zzeneg/zzkeeb/kicad/models/FPC 6-PIN SMD.stp

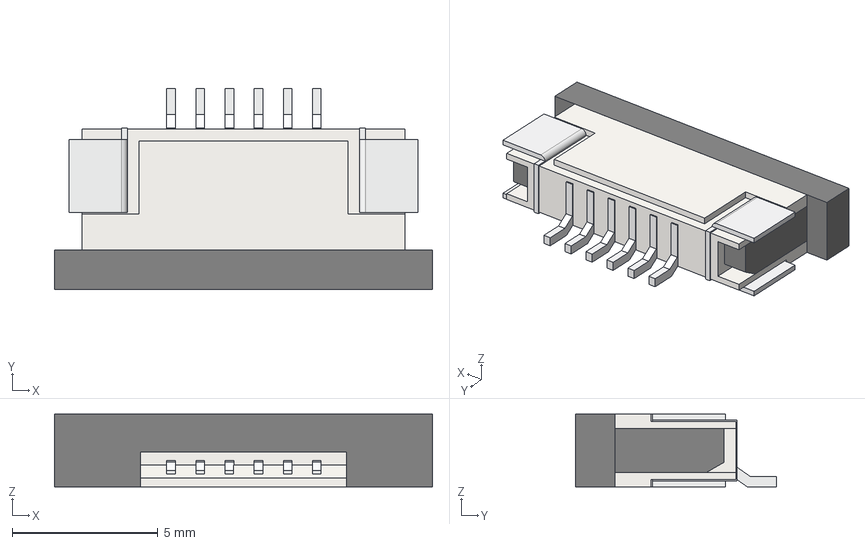
[picture p20: CAD file, 2024-02-03]
kicad/models/FPC 6-PIN SMD.stp
13.0 x 6.90 x 2.50 mm
