zzeneg/zzkeeb/kicad/models/vik-azoteq-adapter-vertical.step

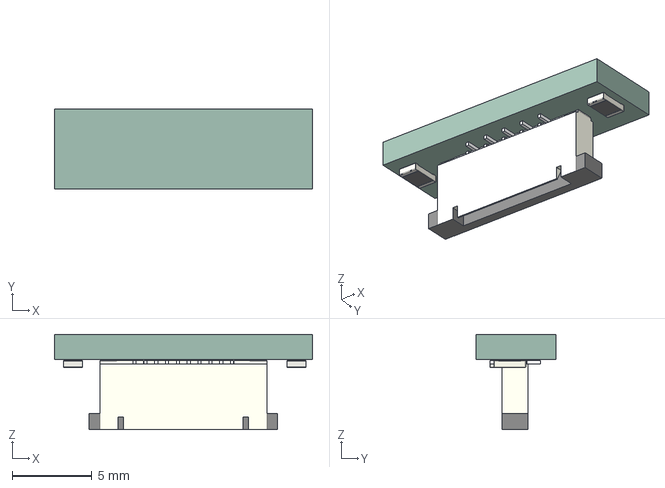
[picture p21: CAD file, 2024-02-03]
kicad/models/vik-azoteq-adapter-vertical.step
16.2 x 5.03 x 5.96 mm
_autosave-azoteq-tps PCB
