zzeneg/zzkeeb/kicad/models/PMW3360 v12.step

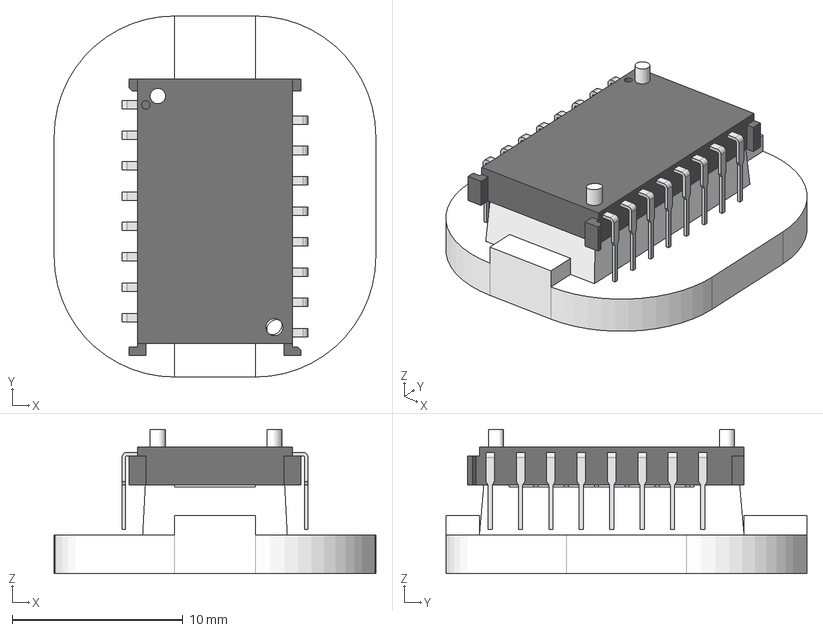
[picture p22: CAD file, 2024-01-15]
kicad/models/PMW3360 v12.step
18.9 x 21.1 x 8.46 mm
Lead x 8
Lead(Mirror) x 8
Lens
