zzeneg/zzkeeb/kicad/models/EC12 Encoder 10mm 3pin.stp

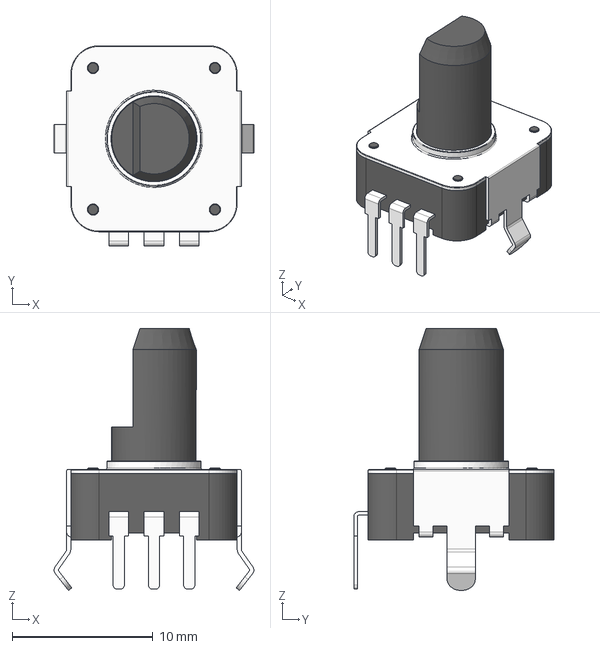
[picture p23: CAD file, 2023-12-11]
kicad/models/EC12 Encoder 10mm 3pin.stp
14.2 x 14.2 x 18.6 mm
