zzeneg/zzkeeb/kicad/models/Button_5way-SKRHABE010-concave-short.step

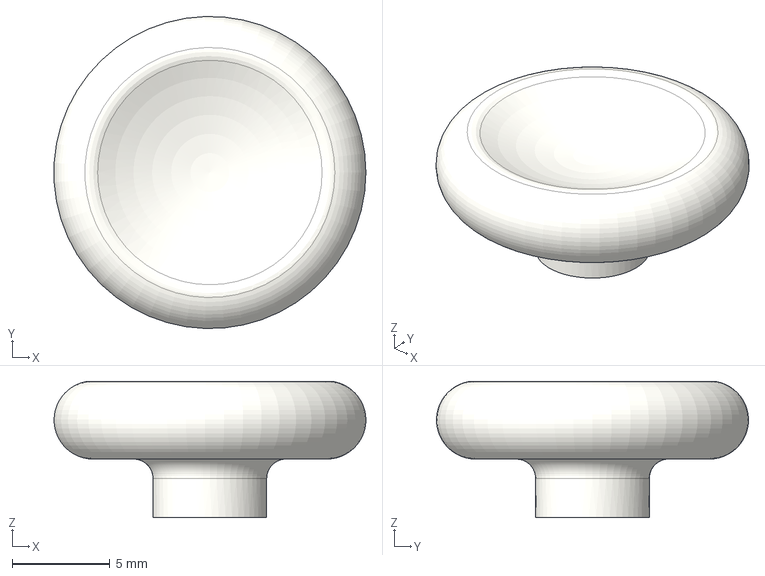
[picture p24: CAD file, 2023-11-05]
kicad/models/Button_5way-SKRHABE010-concave-short.step
16.0 x 16.0 x 6.98 mm
