zzeneg/zzkeeb/kicad/models/Button_5way-SKRHABE010.stp

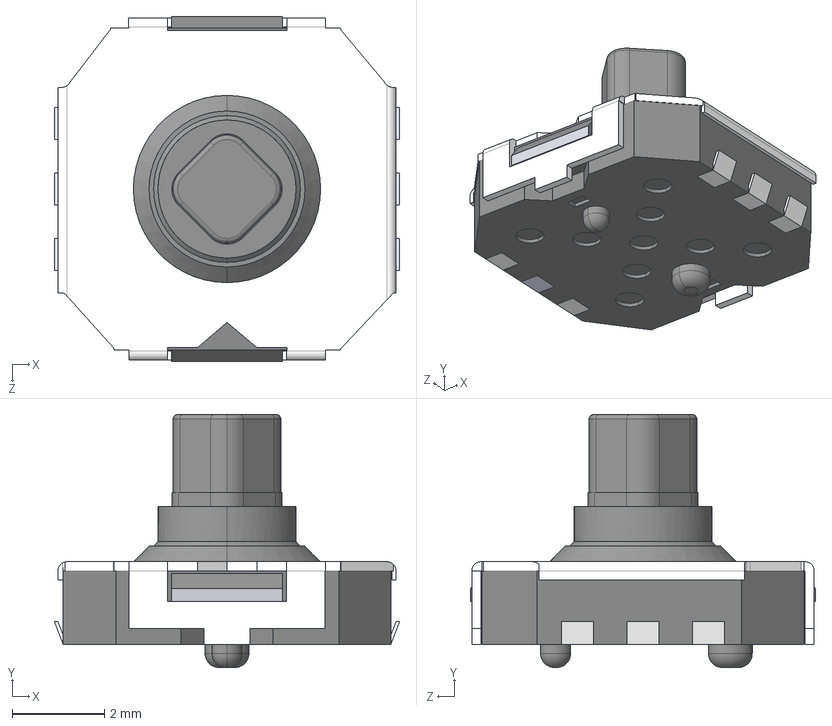
[picture p25: CAD file, 2023-11-05]
kicad/models/Button_5way-SKRHABE010.stp
7.51 x 5.50 x 7.50 mm
