zzeneg/zzkeeb/kicad/models/JST - GH - SMD (V) - 12Pin - 1.25mm.stp

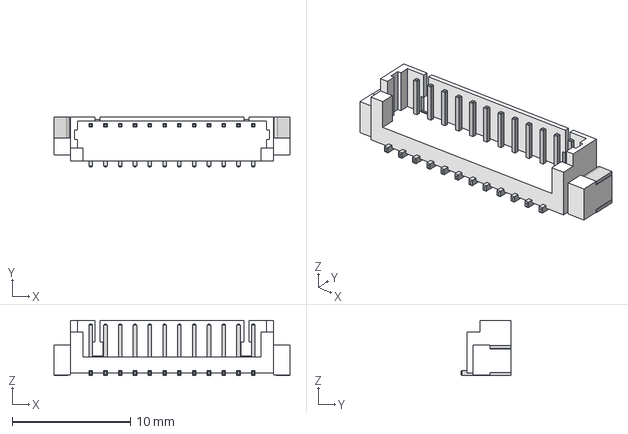
[picture p26: CAD file, 2023-11-02]
kicad/models/JST - GH - SMD (V) - 12Pin - 1.25mm.stp
19.9 x 4.24 x 4.66 mm
