zzeneg/zzkeeb/kicad/models/JST - GH - SMD (R) - 12Pin - 1.25mm.stp

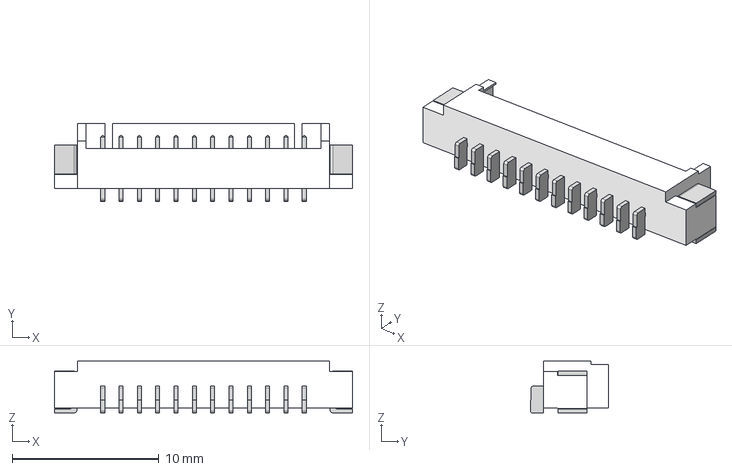
[picture p27: CAD file, 2023-11-02]
kicad/models/JST - GH - SMD (R) - 12Pin - 1.25mm.stp
20.3 x 5.35 x 3.53 mm
