zzeneg/zzkeeb/kicad/models/splinky.step

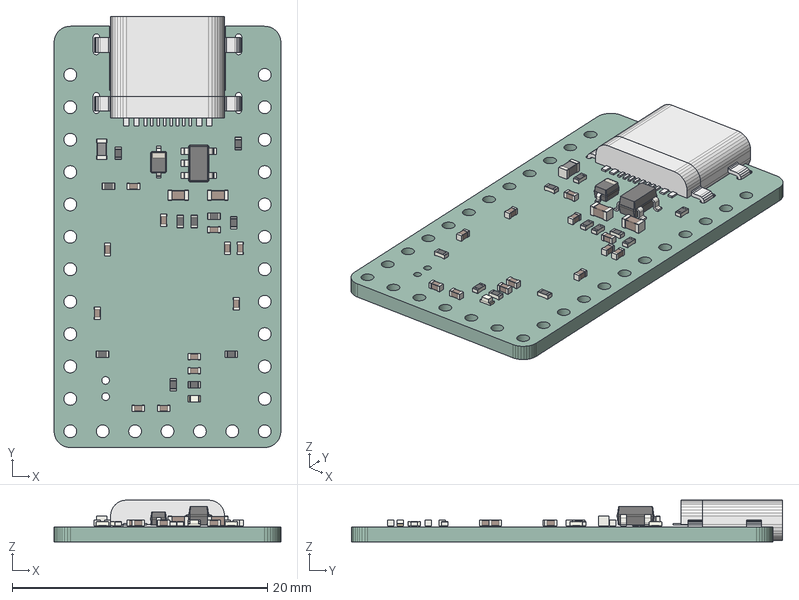
[picture p28: CAD file, 2023-11-01]
kicad/models/splinky.step
17.8 x 33.8 x 3.27 mm
0xB2 PCB
