zzeneg/zzkeeb/kicad/models/niceview.step

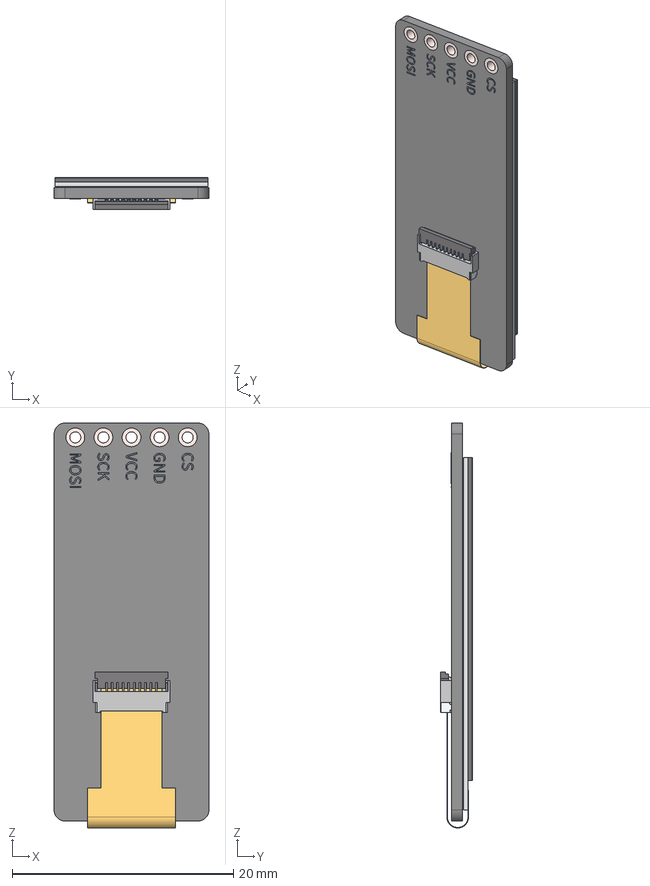
[picture p29: CAD file, 2023-11-01]
kicad/models/niceview.step
14.0 x 2.87 x 36.6 mm
Silkscreen
Screen
FPC
FFC2B28_SP x 2
FFC2B28-10-G_C
FFC2B28-G_P x 10
FFC2B28-10-G_H
FFC2B28-10-G_D
