zzeneg/zzkeeb/kicad/models/5-way-concave-short.step

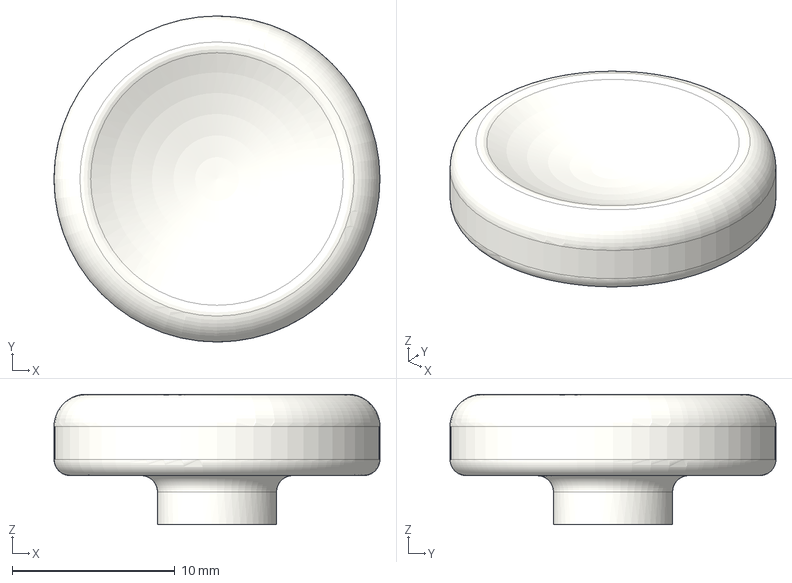
[picture p30: CAD file, 2023-09-16]
kicad/models/5-way-concave-short.step
20.0 x 20.0 x 7.98 mm
