zzeneg/zzkeeb/kicad/models/Magnetic connector 12pin female.step

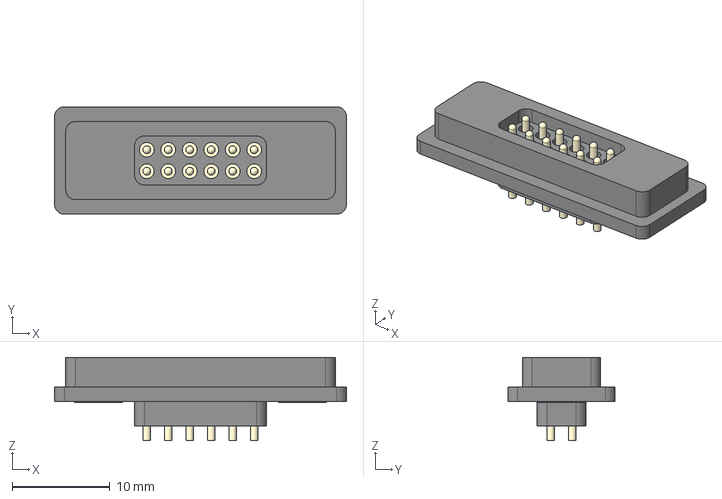
[picture p31: CAD file, 2023-09-04]
kicad/models/Magnetic connector 12pin female.step
29.9 x 11.0 x 8.50 mm
