zzeneg/zzkeeb/kicad/models/Magnetic connector 12pin male.step

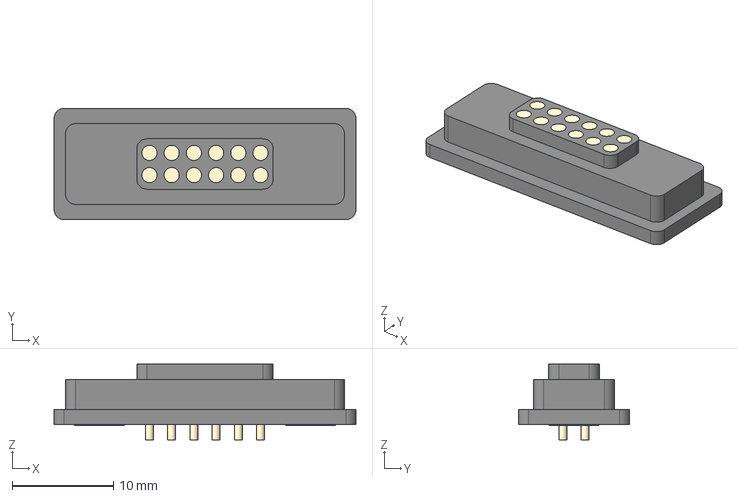
[picture p32: CAD file, 2023-09-04]
kicad/models/Magnetic connector 12pin male.step
29.9 x 11.0 x 7.50 mm
