zzeneg/zzkeeb/kicad/models/5-WayTactileButton10mmTHT.stp

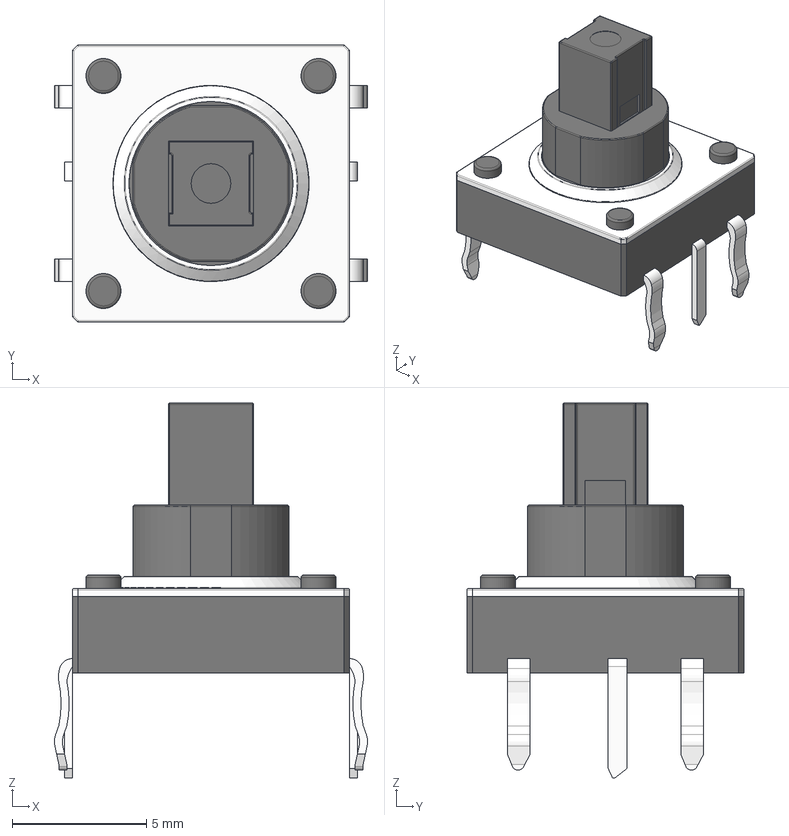
[picture p33: CAD file, 2023-08-19]
kicad/models/5-WayTactileButton10mmTHT.stp
11.6 x 10.3 x 14.0 mm
