zzeneg/zzkeeb/kicad/models/FPC-12.stp

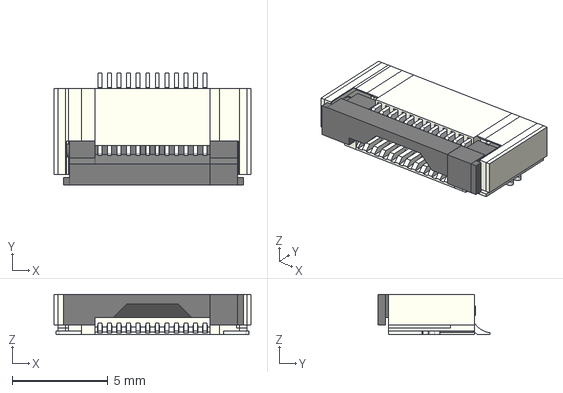
[picture p34: CAD file, 2023-06-14]
kicad/models/FPC-12.stp
10.3 x 5.85 x 2.11 mm
