zzeneg/zzkeeb/kicad/models/c-1-1734742-2-o-3d.stp

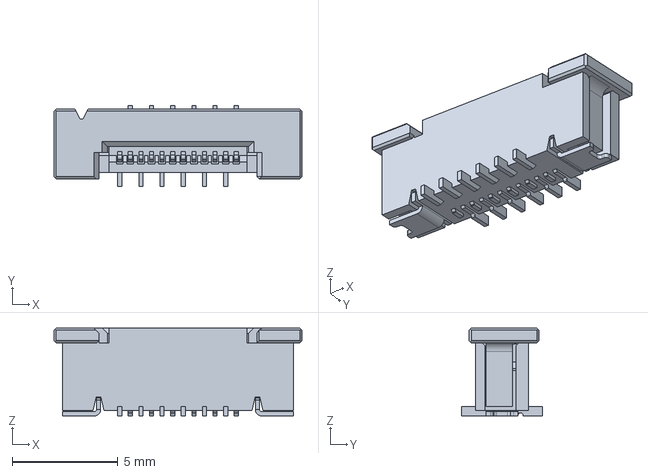
[picture p35: CAD file, 2023-06-14]
kicad/models/c-1-1734742-2-o-3d.stp
11.7 x 3.80 x 4.15 mm
