zzeneg/zzkeeb/kicad/models/ks33_socket.step

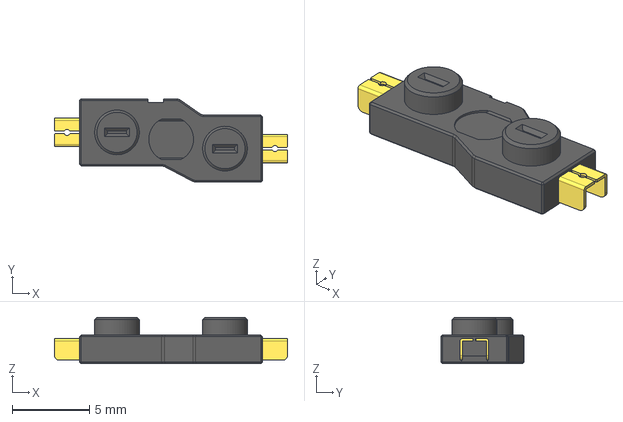
[picture p37: CAD file, 2023-06-05]
kicad/models/ks33_socket.step
15.1 x 5.40 x 3.00 mm
03d659ea-029f-11ee-ae0e-34c93d8226b1_part
03dacb9c-029f-11ee-ae0e-34c93d8226b1_part
