zzeneg/zzkeeb/kicad/models/RotaryEncKnob.STEP

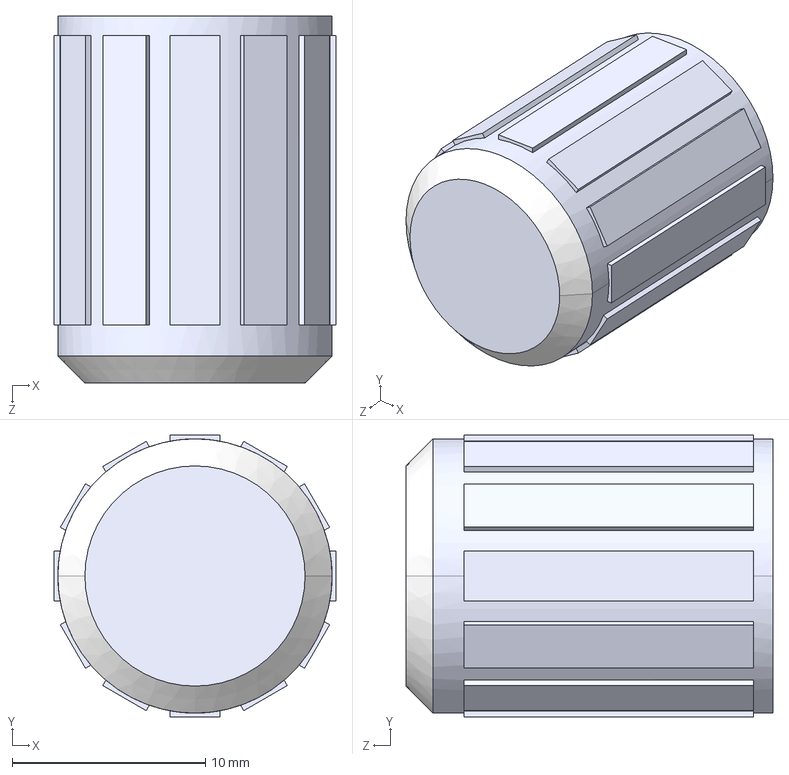
[picture p39: CAD file, 2023-02-26]
kicad/models/RotaryEncKnob.STEP
14.6 x 14.6 x 19.0 mm
