zzeneg/zzkeeb/kicad/models/Display 1.69 ST7789V2.step

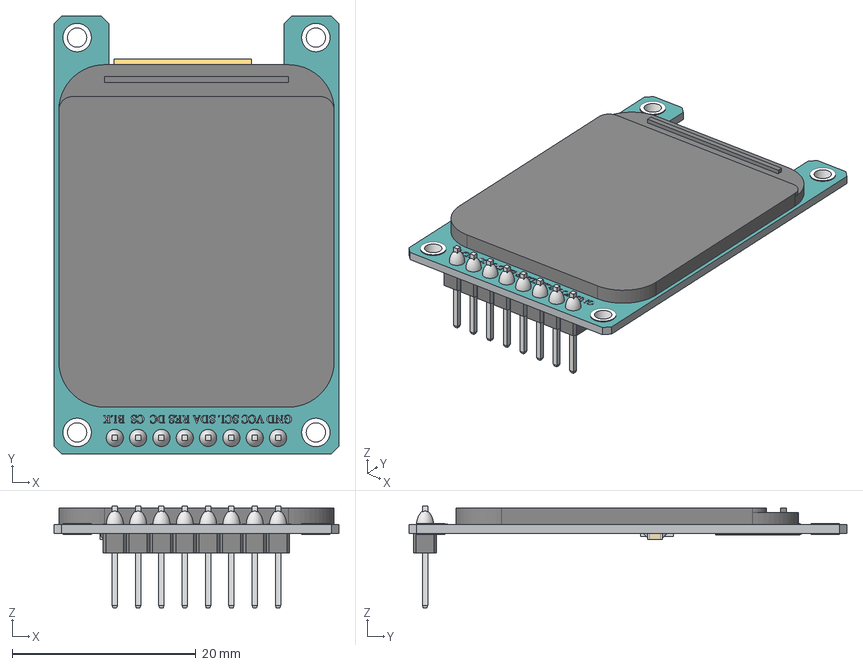
[picture p40: CAD file, 2023-02-21]
kicad/models/Display 1.69 ST7789V2.step
31.0 x 47.7 x 11.1 mm
PCB
Display
Pin x 8
R-0603 x 3
C-0603 x 2
U-0603
