zzeneg/zzkeeb/kicad/models/FPC vertical connector-1mm-10PIN.STEP

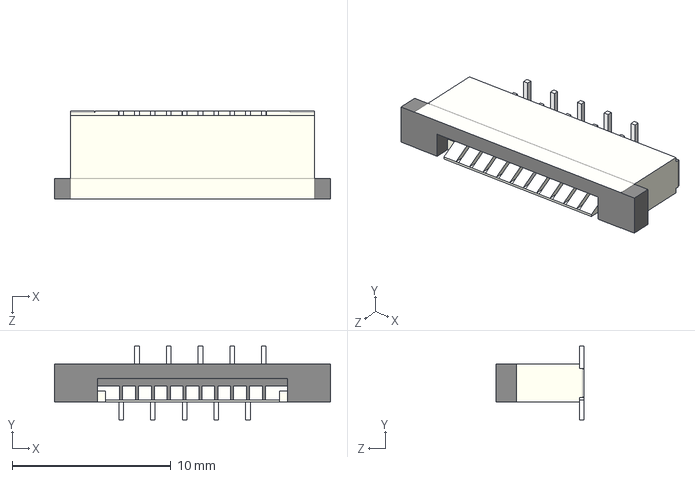
[picture p41: CAD file, 2023-02-21]
kicad/models/FPC vertical connector-1mm-10PIN.STEP
17.4 x 4.64 x 5.55 mm
