zzeneg/zzkeeb/kicad/models/Seeed Studio XIAO RP2040 v26.step

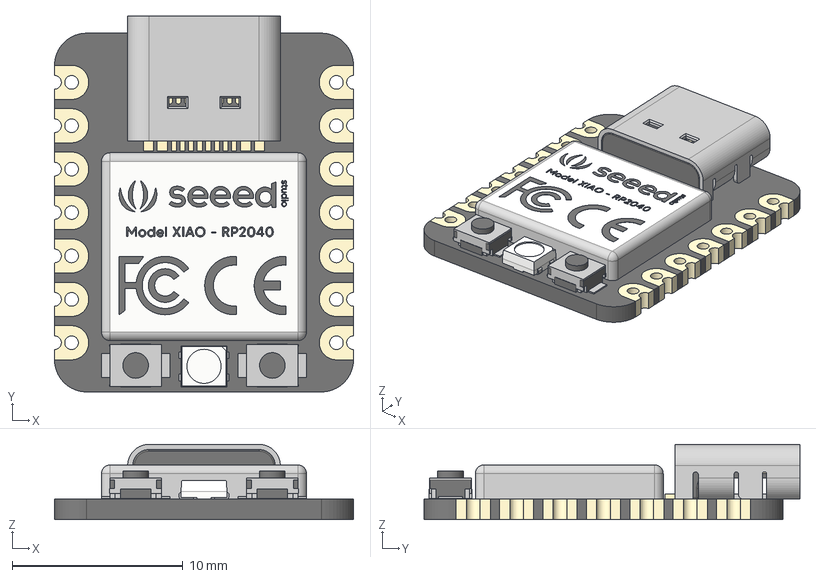
[picture p42: CAD file, 2023-02-16]
kicad/models/Seeed Studio XIAO RP2040 v26.step
17.5 x 22.0 x 4.40 mm
type-c v2
smd_button v3
DOUT
DIN
VSS
VDD
smd_button v3(Mirror)
