zzeneg/zzkeeb/kicad/models/PG1350-socket.STEP

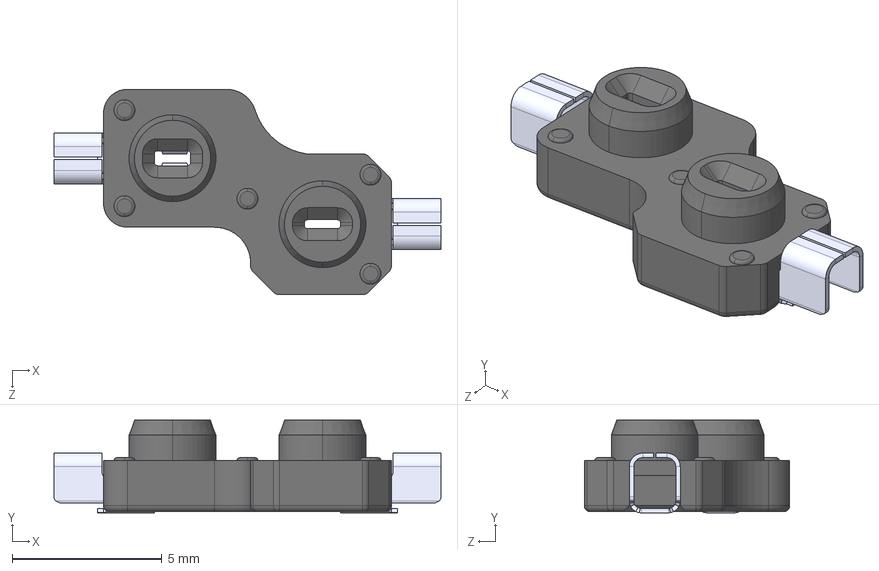
[picture p43: CAD file, 2023-02-04]
kicad/models/PG1350-socket.STEP
12.9 x 3.09 x 6.85 mm
pin x 2
socket
